zuzaniakm/beehive-monitor/beehive_monitor/WiFi.h

#pragma once
#include <WiFi.h>
#include "driver/adc.h"

class Wifi {
  private:
    String _ssid;
    String _password;

  public:
    Wifi() = default;
    int getStatus();
    void setCredentials(String ssid, String password);
    bool connect();
    void disconnect();
    void turnOn();
    void turnOff();
    bool checkConnection();
};

int Wifi::getStatus() {
  return WiFi.status();
}

void Wifi::setCredentials(String ssid, String password) {
  _ssid = ssid;
  _password = password;
}

bool Wifi::connect() {
  if (_ssid == "") { 
    return false; 
  }

  WiFi.begin(_ssid, _password);
  for (unsigned i = 1; i <= 20; i++) {
    if (WiFi.status() == WL_CONNECTED) {
      Serial.println("WiFi connected!");
      Serial.println("IP address: ");
      Serial.println(WiFi.localIP());
      return true;
    } else {
      delay(500);
      Serial.print(".");
    }
  }
  Serial.println("WiFi failed to connect!");
  WiFi.disconnect();
  return false;
}

void Wifi::disconnect() {
  WiFi.disconnect(true);
}

void Wifi::turnOff() {
  if (WiFi.status() != WL_NO_SHIELD) {
    adc_power_off();
    WiFi.disconnect(true);
    WiFi.mode(WIFI_OFF);
  }
}

void Wifi::turnOn() {
  if (WiFi.status() == WL_NO_SHIELD) {
    adc_power_on();
    WiFi.enableSTA(true);
    WiFi.mode(WIFI_STA);
  }
}

bool Wifi::checkConnection() {
  int status = WiFi.status();
  if (status == WL_CONNECTED) {
    return true;
  }
  if (status == WL_NO_SHIELD) {
    turnOn();
  }
  return connect();
}
